Skyhawkson/Pyro-Test-Board/Pyro Tester Rev1.0.0/SPICE Sims/ACS711_DarlingtonPair_Sim.asc

C1: cap; 1µF
I1: current; 5
Q1: npn; FZT849
Q2: npn; LS301
R1: res; .5R
R2: res; 1.2mR
R3: res; 1.01R
R4: res; 100R
R5: res; 1000R
R6: res; 8090R
R7: res; 1000R
R8: res; 215.686R
R9: res; 1000R
U1: opamp
U2: UniversalOpamp2; Avol=1Meg GBW=3Meg Slew=20Meg
U3: UniversalOpamp2
U4: UniversalOpamp2
U5: UniversalOpamp2
V1: voltage; PULSE(0 5 0 .00001 0 .005 1 1)
V2: voltage; 12
V3: voltage; 12V
Named nets: 0, FB, SIG, ACSOUT, PREBUF, SENSEH, SENSEL, CTRL, CTRL3, 5V
.tran .01
.inc opamp.sub
Gain and Buffer to
approximate ACS711
Opamp with 
gain 9.09
LPF for Smoothing?
Input: 1-5V
Output: 1-5A
OPAMP Power labelled "5V" is actually running at 12V
