Skyhawkson/Pyro-Test-Board/Pyro Tester Rev1.0.0/SPICE Sims/DarlingtonPairPractice.asc

Q1: npn; FZT849
Q2: npn; 2N2222
R1: res; 1R
R2: res; 50R
U1: opamp
U2: opamp
V1: voltage; 28
V2: voltage; SINE(2.5 2.5 1)
Named nets: 0
.tran 1
V needs to be at least 28VDC to do 5A at 5V
