Skyhawkson/Pyro-Test-Board/Pyro Tester Rev1.0.0/SPICE Sims/Diff_Amp.asc

Q1: npn; FZT849
Q2: npn; 2N2222
R1: res; .1R
R2: res; 5R
U1: opamp
U2: opamp
V1: voltage; 1
V2: signal; PULSE(0 3.3 0 0 0 .0004 .0005)
V3: voltage; 12
Named nets: 0
.tran 1
