Skyhawkson/Pyro-Test-Board/Pyro Tester Rev1.0.0/SPICE Sims/Diff_Amp_2_Ramp_Test.asc

C1: cap; 1µF
R1: res; 1000R
R2: res; 130R
R11: res; 49.9R
R12: res; 220R; tol=1
R13: res; 1000R
R14: res; 1500R; tol=1
U1: UniversalOpamp2
U4: UniversalOpamp2
V1: voltage; 1.1
V2: voltage; 12
V4: voltage; 1.8V
V5: voltage; PULSE(1.65 2.31 0 .1 0 .005 1 1)
Named nets: 0, 12V, VREF, VOUT, VRAMP, VCTRL, VCMD
.tran .25
.inc opamp.sub
OpAmp Power
Sim Settings
CMD/FB Comparator Amp
Diff Amp being Simulated
