Skyhawkson/Pyro-Test-Board/Pyro Tester Rev1.0.0/SPICE Sims/Power_Transistor_Take_3.asc

C1: cap; 10µF
L1: ind; 250m; Rser=0 Rpar=0
M1: nmos; 2N7002
Q2: npn
R1: res; 1000R
R2: res; 25R
R3: res; 1
V1: voltage; 12V
V2: voltage; PULSE(0 12 0 0 0 .0003 .0005 500)
V3: voltage; 12V
Named nets: 0
.tran 1
I don't get why I need to drive this at 12V to switch 50mA.
R2 should be a trimpot on the dev board
Consider forward voltages of FET and transistor
Darlington-pair the transistor (keeping forward voltages in mind?
