Skyhawkson/Pyro-Test-Board/Pyro Tester Rev1.0.0/SPICE Sims/PWM_5A_Test.asc

C1: cap; .0012
L1: ind; 4700µ; Ipk=7 Rser=0.0774 Rpar=52752 Cpar=0
M1: nmos; BSC118N10NS
R1: res; .1
R2: res; 2
V1: voltage; 12
V2: voltage; PULSE(0 48 0 0 0 0.00045 0.0005 500)
Named nets: 0, CTRL, PREAMP, POSTAMP
.tran 1
Need a way to sink the extra current to ground, I think
Will need flyback diodes to handle voltage spikes if R2 opens, and should also use that event to close M1
