Skyhawkson/Pyro-Test-Board/Pyro Tester Rev1.0.0/SPICE Sims/PWM_5A_Test_PowerTransistor.asc

C1: cap; .0012
M2: nmos; Si7336ADP
Q1: npn; 2SC4102
Q2: npn; FZT849
R1: res; .1
R2: res; 2
R3: res; 9000
V1: voltage; 12
V2: voltage; PULSE(0 48 0 0 0 0.00004 0.00005 500)
V3: voltage; 12
Named nets: 0, PREAMP, POSTAMP, CTRL, BASE
.tran 1
Need a way to sink the extra current to ground, I think
Will need flyback diodes to handle voltage spikes if R2 opens, and should also use that event to close M1
Plan: Final transistor has gain of 100. Need 5A, so need to provide ~50mV. Inductance is a pain; going to use a darlington pair.
2N3904 has gain of 40. Need to provide 1.25mA.
